MelansonTech/Heart-Beatz/chassis/123d/Rev 7/rev 7 work space/plate rev 7 thicker.stl

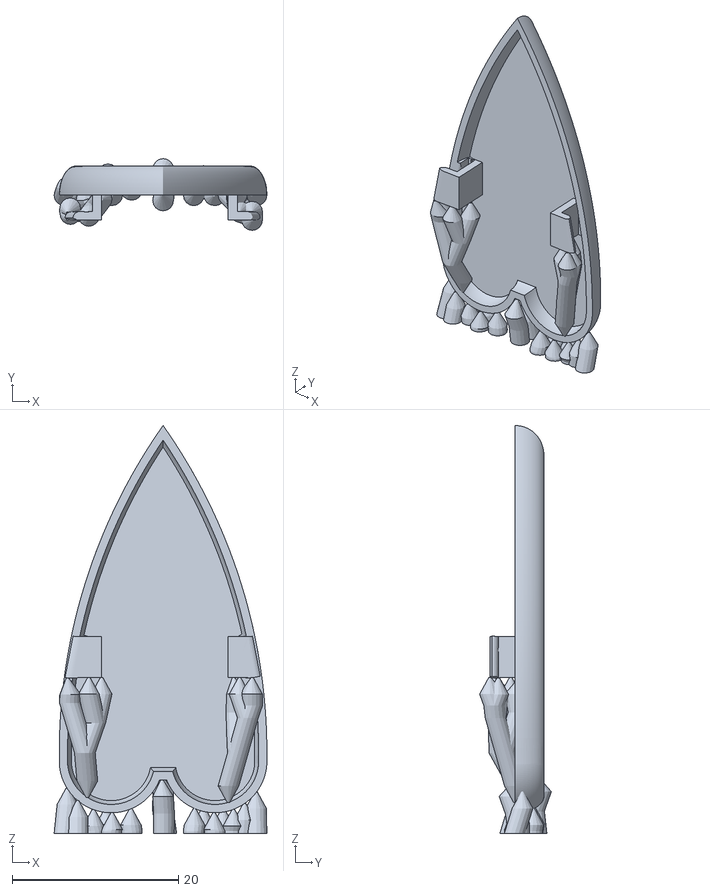
[picture p17: CAD file, 2025-01-01]
chassis/123d/Rev 7/rev 7 work space/plate rev 7 thicker.stl
25.6 x 8.64 x 49.1
