MelansonTech/Heart-Beatz/chassis/123d/Rev 8 final/STLs/cover support test 1-1.stl

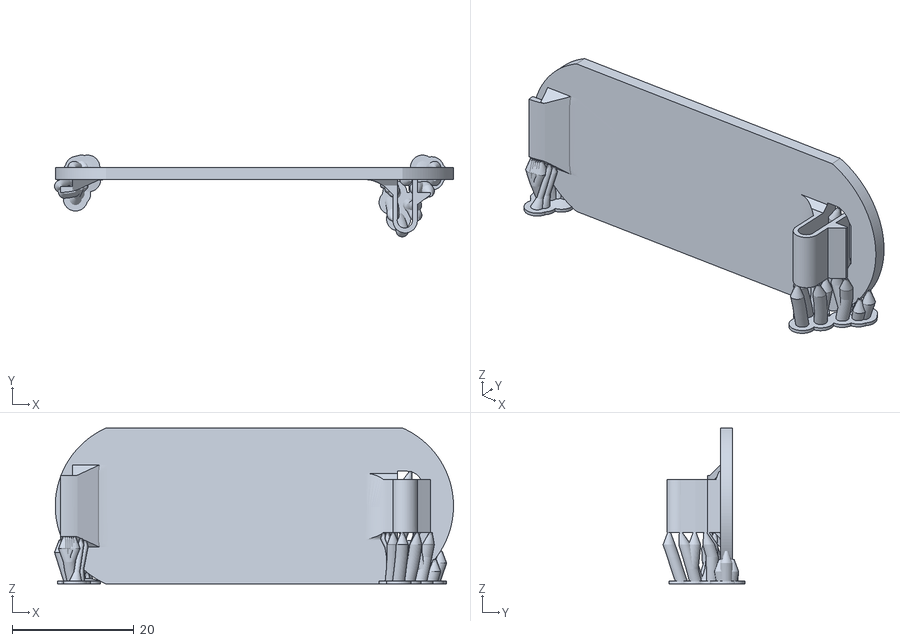
[picture p18: CAD file, 2025-01-01]
chassis/123d/Rev 8 final/STLs/cover support test 1-1.stl
65.5 x 13.5 x 25.6
