MelansonTech/Heart-Beatz/chassis/Remodel/test prints/pcb1mm.stl

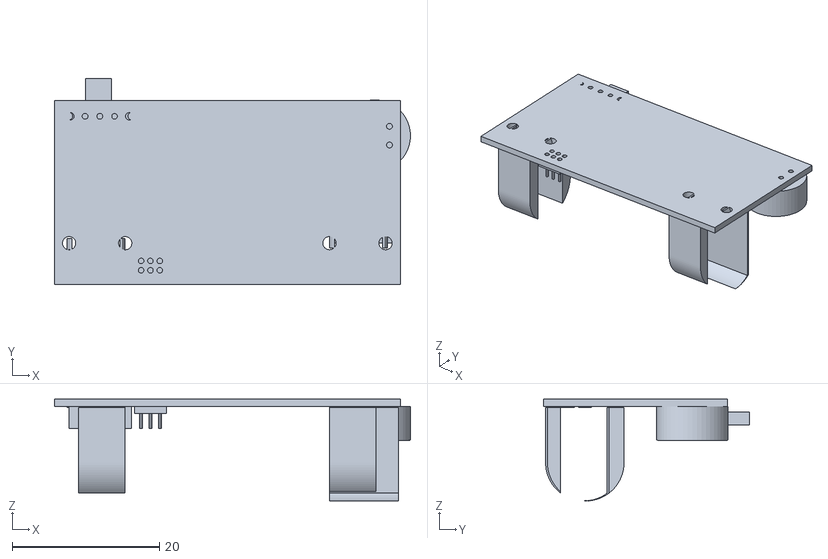
[picture p19: CAD file, 2025-01-01]
chassis/Remodel/test prints/pcb1mm.stl
48.4 x 28.0 x 13.8
