MelansonTech/Heart-Beatz/chassis/123d/Rev 7/rev 7 work space/plate rev 7.stl

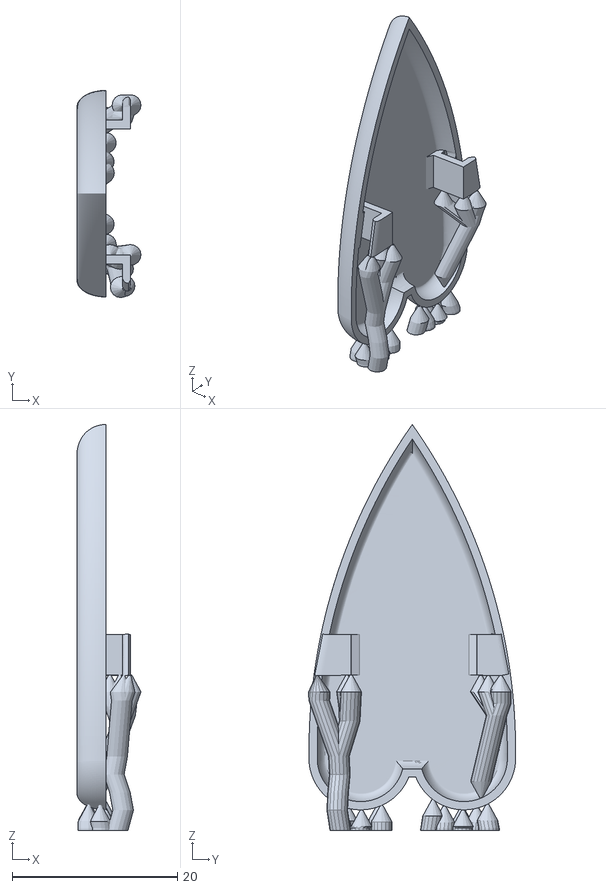
[picture p20: CAD file, 2025-01-01]
chassis/123d/Rev 7/rev 7 work space/plate rev 7.stl
7.75 x 25.1 x 49.1
