MelansonTech/Heart-Beatz/chassis/Remodel/test prints/cover 3.stl

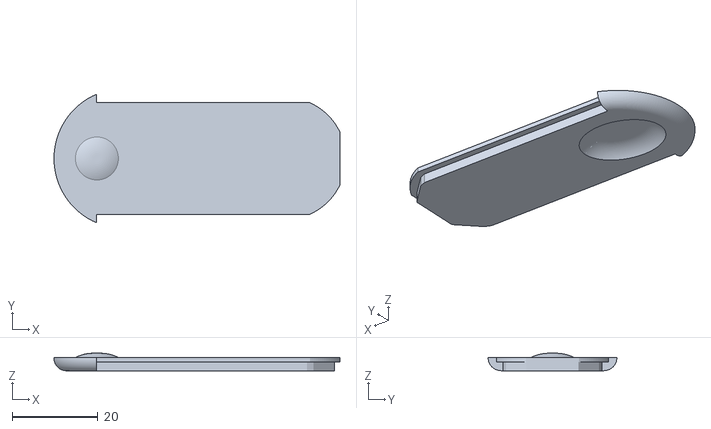
[picture p21: CAD file, 2025-01-01]
chassis/Remodel/test prints/cover 3.stl
66.6 x 30.0 x 4.10
