MelansonTech/Heart-Beatz/chassis/STLs/Rev 3.0/Customizeable Plate.stl

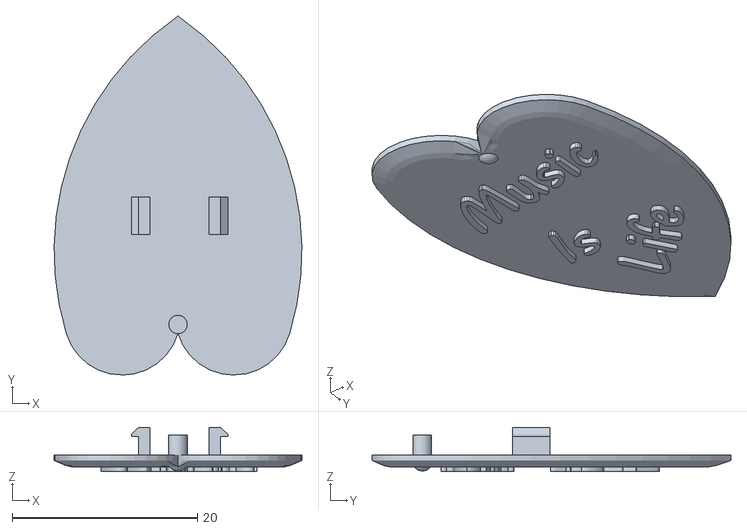
[picture p22: CAD file, 2025-01-01]
chassis/STLs/Rev 3.0/Customizeable Plate.stl
26.8 x 38.8 x 4.76
