MelansonTech/Heart-Beatz/chassis/Remodel/test prints/heart.stl

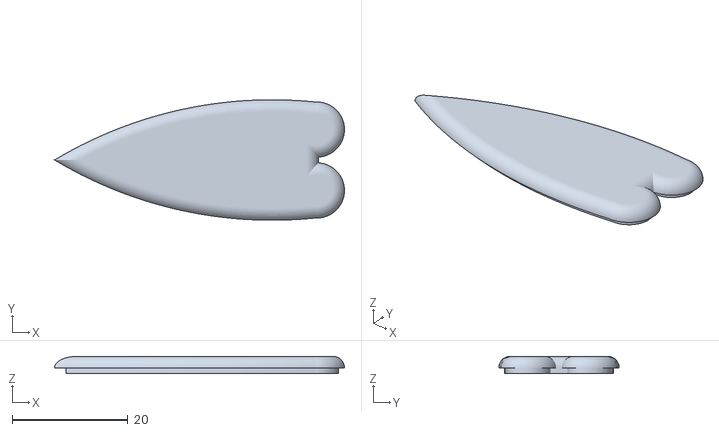
[picture p23: CAD file, 2025-01-01]
chassis/Remodel/test prints/heart.stl
50.0 x 20.8 x 3.00
