MelansonTech/Heart-Beatz/chassis/123d/Rev 7/rev 7 work space/plate rev 7 thicker 2 with struts.stl

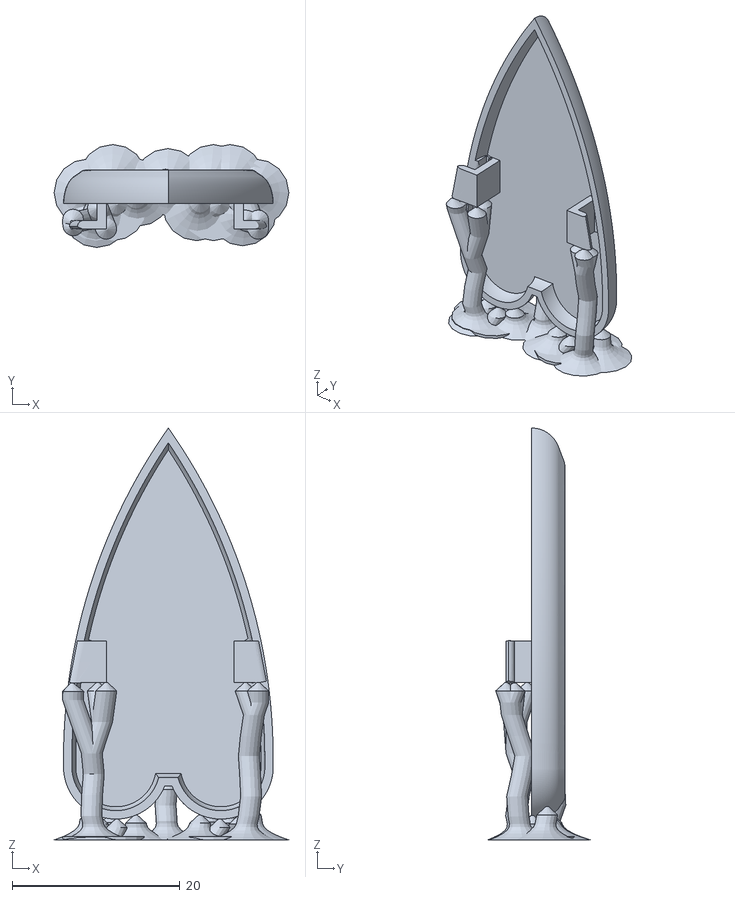
[picture p24: CAD file, 2025-01-01]
chassis/123d/Rev 7/rev 7 work space/plate rev 7 thicker 2 with struts.stl
28.0 x 12.3 x 49.1
