MelansonTech/Heart-Beatz/chassis/123d/Rev 7/rev 7 work space/plate rev7-3struts.stl

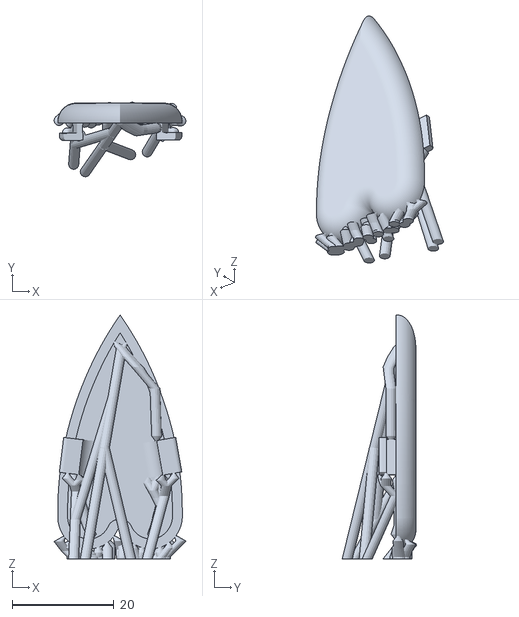
[picture p25: CAD file, 2025-01-01]
chassis/123d/Rev 7/rev 7 work space/plate rev7-3struts.stl
25.9 x 14.7 x 47.9
