MelansonTech/Heart-Beatz/chassis/123d/Rev 7/rev 7 work space/chassis rev 7.stl

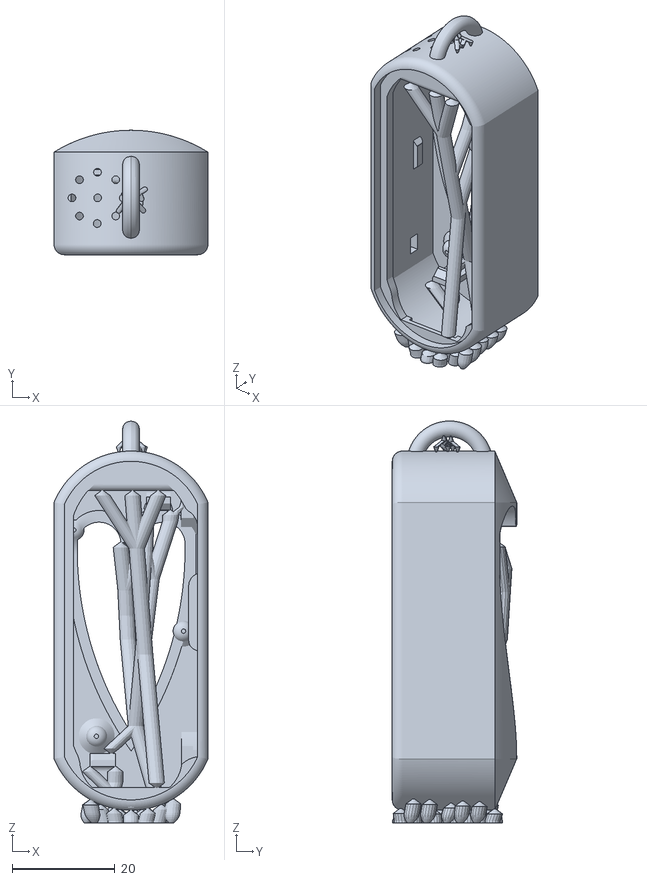
[picture p26: CAD file, 2025-01-01]
chassis/123d/Rev 7/rev 7 work space/chassis rev 7.stl
30.0 x 24.3 x 78.4
