MelansonTech/Heart-Beatz/chassis/123d/Rev 7/rev 7 work space/chassisredo.stl

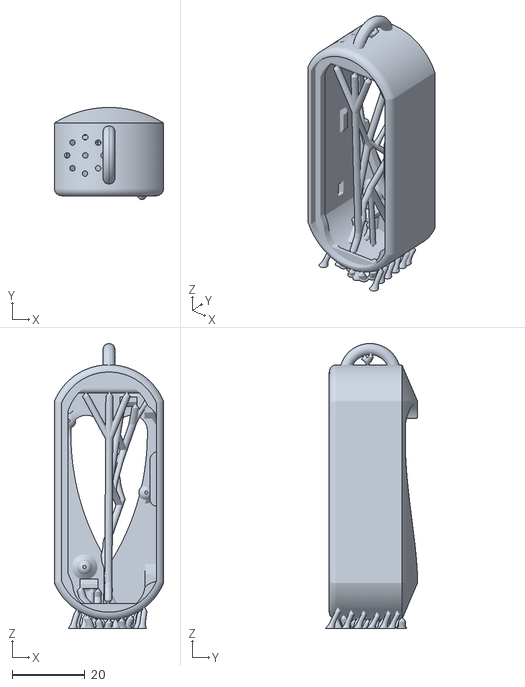
[picture p27: CAD file, 2025-01-01]
chassis/123d/Rev 7/rev 7 work space/chassisredo.stl
30.0 x 25.3 x 78.4
