MelansonTech/Heart-Beatz/chassis/New Concept/Blinky Chassis A rev 6.stl

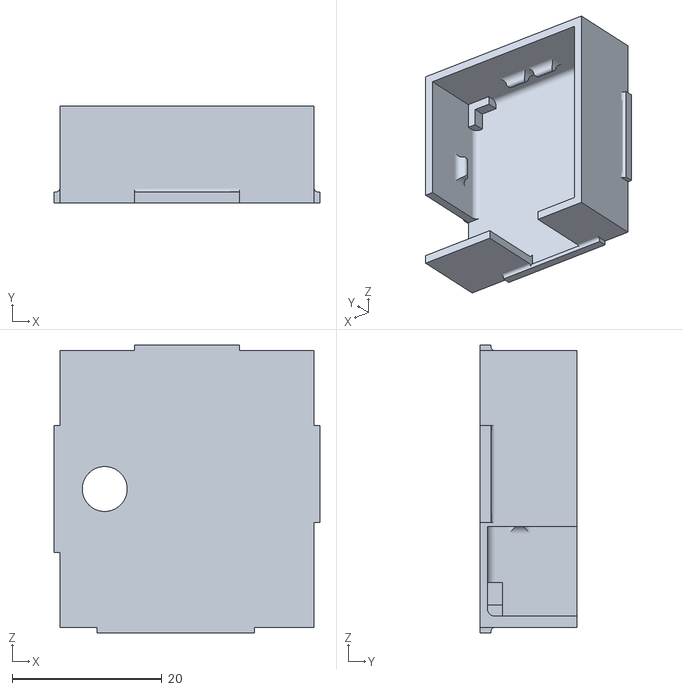
[picture p28: CAD file, 2025-01-01]
chassis/New Concept/Blinky Chassis A rev 6.stl
35.5 x 13.0 x 38.5
