MelansonTech/Heart-Beatz/code/blinky Code Rev5/blinky Code Rev5/main.cfg

/**
 *  @fileOverview Grace
 */

/* need to use the CSL module to generate the CSL code */
var CSL = xdc.useModule('ti.mcu.msp430.csl.CSL');
var ADC10 = xdc.useModule('ti.mcu.msp430.csl.adc.ADC10');
var Timer0_A3 = xdc.useModule('ti.mcu.msp430.csl.timer.Timer0_A3');
var Timer1_A3 = xdc.useModule('ti.mcu.msp430.csl.timer.Timer1_A3');
CSL.configApiVersion = "1.20.00";

/* these modules should be part of every project */
var BCSplus = xdc.useModule('ti.mcu.msp430.csl.clock.BCSplus');
var WDTplus = xdc.useModule('ti.mcu.msp430.csl.watchdog.WDTplus');
var System = xdc.useModule('ti.mcu.msp430.csl.system.System');
var GPIO = xdc.useModule('ti.mcu.msp430.csl.gpio.GPIO');
var InterruptVectors = xdc.useModule('ti.mcu.msp430.csl.interrupt_vectors.InterruptVectors');

/* set stack and heap sizes as appropriate for MSP430 */
Program.sysStack = 0;
Program.stack = 64;
Program.heap = 0;
Program.argSize = 0;

/* Enable global interrupt */
System.srRegs.SR.GIE = System.srDefs.GIE;
BCSplus.userInputDCO = 8000.0;
BCSplus.regs.DCOCTL.DCO1 = BCSplus.defs.DCO1_OFF;
BCSplus.regs.BCSCTL1.RSEL3 = BCSplus.defs.RSEL3_OFF;
BCSplus.regs.BCSCTL1.RSEL0 = BCSplus.defs.RSEL0_OFF;
BCSplus.regs.DCOCTL.MOD3 = BCSplus.defs.MOD3_OFF;
BCSplus.regs.DCOCTL.MOD2 = BCSplus.defs.MOD2;
BCSplus.regs.DCOCTL.MOD1 = BCSplus.defs.MOD1_OFF;
BCSplus.regs.DCOCTL.MOD0 = BCSplus.defs.MOD0_OFF;
ADC10.regs.ADC10AE0 = 32;
ADC10.regs.ADC10CTL1.INCH = ADC10.defs.INCH_5;
ADC10.regs.ADC10CTL0.ADC10ON = ADC10.defs.ADC10ON;
ADC10.regs.ADC10CTL0.REFON = ADC10.defs.REFON;
ADC10.regs.ADC10CTL0.SREF = ADC10.defs.SREF_1;
GPIO.regs.P1DIR.Bit0 = GPIO.defs.BIT0;
GPIO.regs.P1DIR.Bit6 = GPIO.defs.BIT6;
Timer0_A3.regs.TA0CTL.ID = Timer0_A3.defs.ID_1;
Timer0_A3.regs.TA0CTL.TASSEL = Timer0_A3.defs.TASSEL_2;
Timer0_A3.inputClockToTimer = 8000.0;
Timer0_A3.inClkPin[0] = 0;
Timer0_A3.txClkPin[0] = 0;
Timer0_A3.regs.interruptSource[1].interruptEnable = true;
Timer0_A3.regs.interruptSource[1].interruptHandler = true;
Timer0_A3.regs.TA0CCTL0.CCIE = Timer0_A3.defs.CCIE;
Timer0_A3.regs.TA0CCR0 = 6666;
Timer0_A3.regs.TA0CTL.MC = Timer0_A3.defs.MC_1;
CSL.device.vcc = 3.3;
BCSplus.regs.DCOCTL.DCO0 = BCSplus.defs.DCO0_OFF;
BCSplus.regs.BCSCTL1.RSEL2 = BCSplus.defs.RSEL2_OFF;
BCSplus.regs.BCSCTL1.RSEL1 = BCSplus.defs.RSEL1_OFF;
ADC10.regs.ADC10CTL0.ADC10SHT = ADC10.defs.ADC10SHT_3;
Timer1_A3.regs.TA1CTL.TASSEL = Timer1_A3.defs.TASSEL_1;
Timer1_A3.txClkPin[0] = 0;
Timer1_A3.inputClockToTimer = 12.0;
Timer1_A3.regs.TA1CTL.ID = Timer1_A3.defs.ID_3;
Timer1_A3.regs.TA1CCR0 = 600;
Timer1_A3.regs.interruptSource[1].interruptEnable = true;
Timer1_A3.regs.interruptSource[1].interruptHandler = true;
Timer1_A3.regs.TA1CCTL0.CCIE = Timer1_A3.defs.CCIE;
Timer1_A3.regs.TA1CTL.MC = Timer1_A3.defs.MC_1;
GPIO.regs.P1DIR.Bit4 = GPIO.defs.BIT4;
Timer1_A3.inClkPin[0] = 0;
Timer0_A3.ccrXTimerSelection_PowerUser[1] = xdc.module("ti.mcu.msp430.csl.timer.ITimer").CCRxTimerSelection_PowerUser_Selection_0;
Timer0_A3.ccrXTimerSelection_BasicView[1] = xdc.module("ti.mcu.msp430.csl.timer.ITimer").CCRxTimerSelection_BasicView_Selection_0;
Timer0_A3.ccInputPin[2] = 0;
Timer0_A3.regs.TA0CCR1 = 0;
Timer0_A3.ccrOutputPin[2] = 0;
Timer0_A3.regs.interruptSource[2].interruptEnable = false;
Timer0_A3.regs.interruptSource[2].interruptHandler = true;
Timer0_A3.regs.interruptSource[0].interruptHandler = true;
Timer0_A3.regs.interruptSource[3].interruptHandler = true;
Timer0_A3.regs.TA0CCTL1.CCIE = Timer0_A3.defs.CCIE_OFF;
GPIO.regs.P1DIR.Bit7 = GPIO.defs.BIT7;
GPIO.regs.P2DIR.Bit4 = GPIO.defs.BIT4;
ADC10.regs.ADC10CTL1.ADC10SSEL = ADC10.defs.ADC10SSEL_0;
ADC10.regs.ADC10CTL1.SHS = ADC10.defs.SHS_0;
